ChipCE/Bear-upgrade-snakeoil-mod/4020-fan-bearmera/step/body-front.step

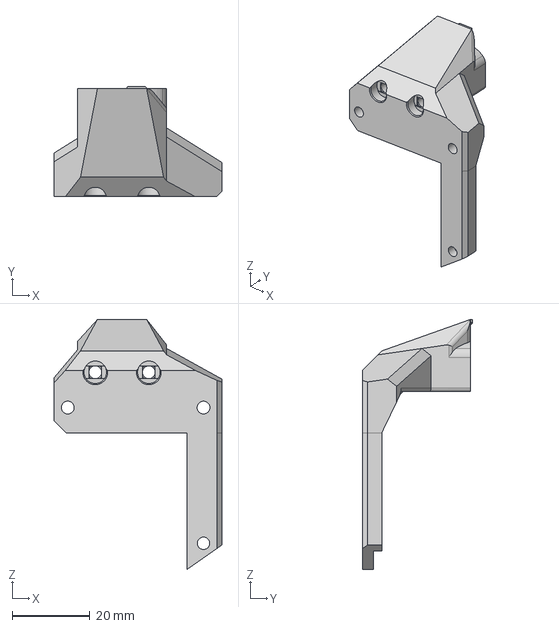
[picture p15: CAD file, 2020-04-13]
4020-fan-bearmera/step/body-front.step
43.2 x 28.4 x 64.5 mm
