ChipCE/Bear-upgrade-snakeoil-mod/BMG extruder/v2/stl/v2-hingle.stl

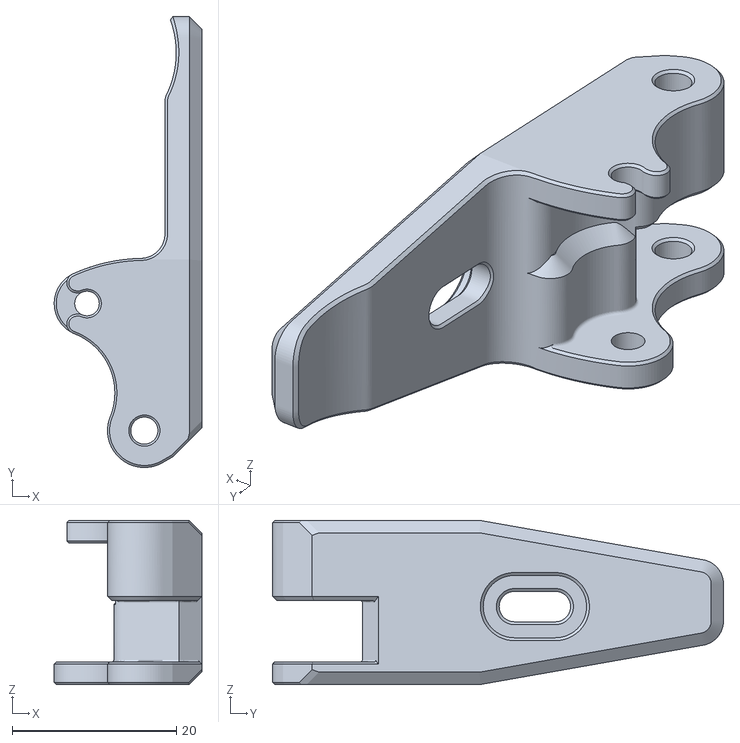
[picture p16: CAD file, 2020-04-23]
BMG extruder/v2/stl/v2-hingle.stl
18.0 x 55.0 x 20.0
