ChipCE/Bear-upgrade-snakeoil-mod/Linear-rail/Bear-frame/12h-block-mount.stl

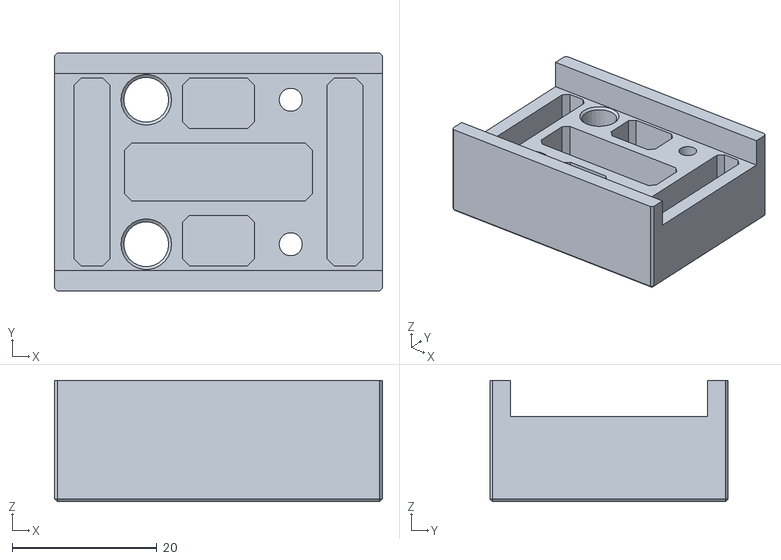
[picture p17: CAD file, 2020-05-15]
Linear-rail/Bear-frame/12h-block-mount.stl
45.4 x 33.0 x 16.8
