ChipCE/Bear-upgrade-snakeoil-mod/Linear-rail/Original-mk3-frame/v2/step/head-rev2.step

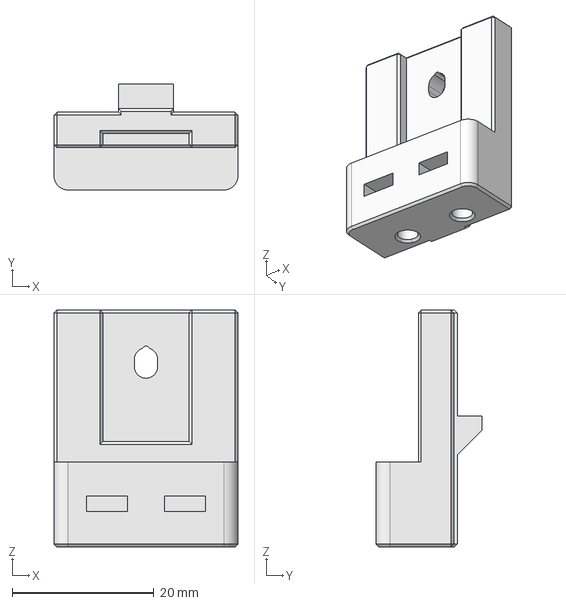
[picture p18: CAD file, 2020-04-23]
Linear-rail/Original-mk3-frame/v2/step/head-rev2.step
26.0 x 15.0 x 33.5 mm
