ChipCE/Bear-upgrade-snakeoil-mod/Y-end-stop/step/y-end-stop-cap.step

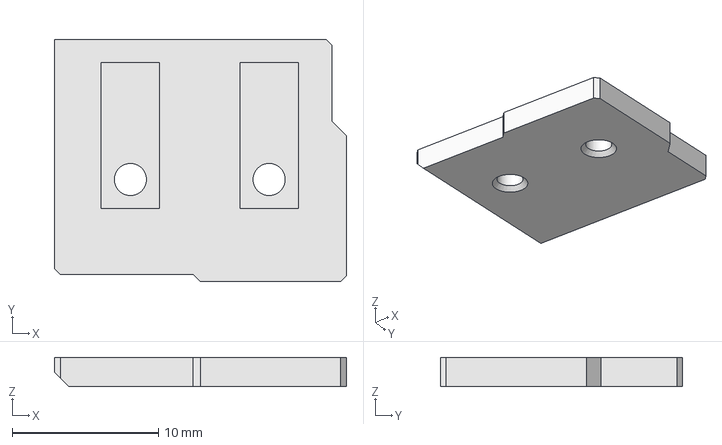
[picture p19: CAD file, 2020-04-13]
Y-end-stop/step/y-end-stop-cap.step
20.0 x 16.6 x 2.00 mm
