ChipCE/Bear-upgrade-snakeoil-mod/Y-idler-tensioner/step/base.step

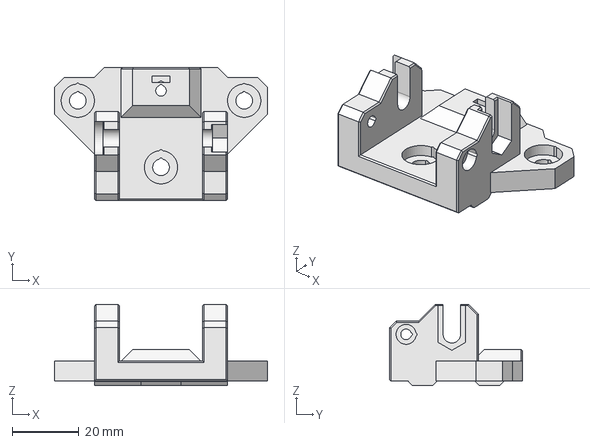
[picture p20: CAD file, 2020-04-13]
Y-idler-tensioner/step/base.step
64.0 x 40.0 x 24.4 mm
