ChipCE/Bear-upgrade-snakeoil-mod/4020-fan-bearmera/step/fan-duct.step

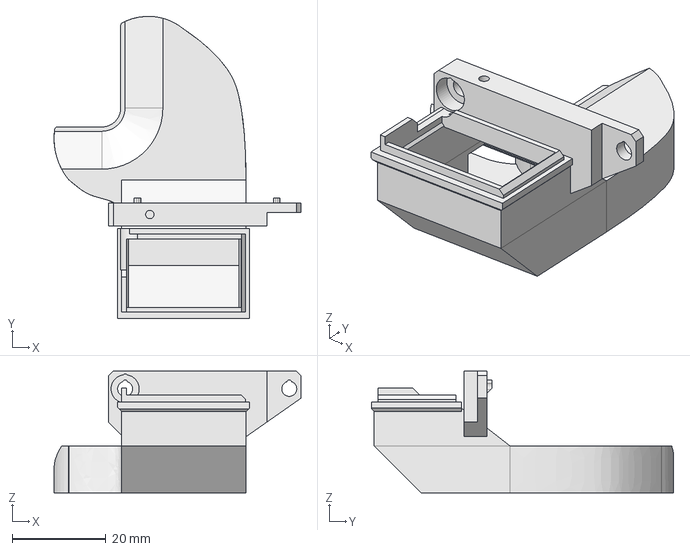
[picture p21: CAD file, 2020-04-13]
4020-fan-bearmera/step/fan-duct.step
52.7 x 64.5 x 26.0 mm
