ChipCE/Bear-upgrade-snakeoil-mod/BMG extruder/v2/stl/v2-Sensor_Cover_MK3s-M6x1.STL

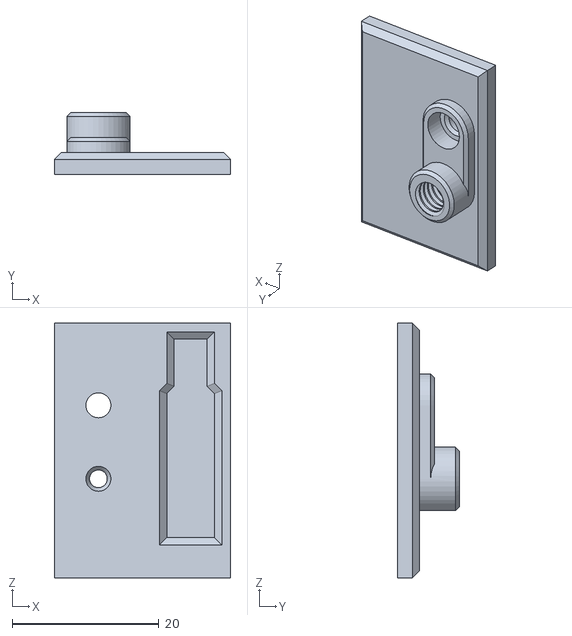
[picture p22: CAD file, 2020-04-23]
BMG extruder/v2/stl/v2-Sensor_Cover_MK3s-M6x1.STL
24.0 x 8.40 x 34.7
