ChipCE/Bear-upgrade-snakeoil-mod/Linear-rail/Bear-frame/head-tail.stl

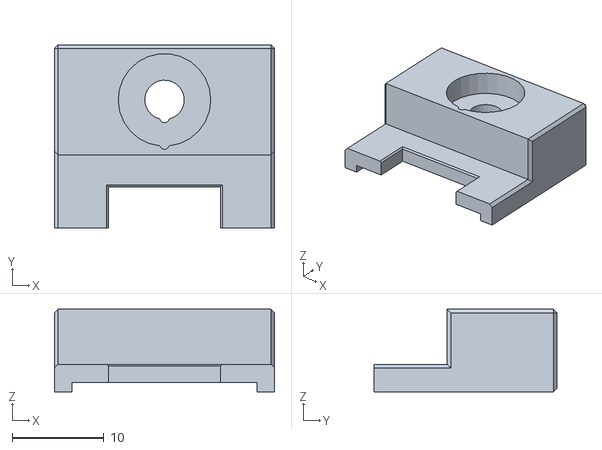
[picture p23: CAD file, 2020-04-13]
Linear-rail/Bear-frame/head-tail.stl
24.0 x 20.0 x 9.00
