ChipCE/Bear-upgrade-snakeoil-mod/Linear-rail/Original-mk3-frame/v2/step/tail-rev2.step

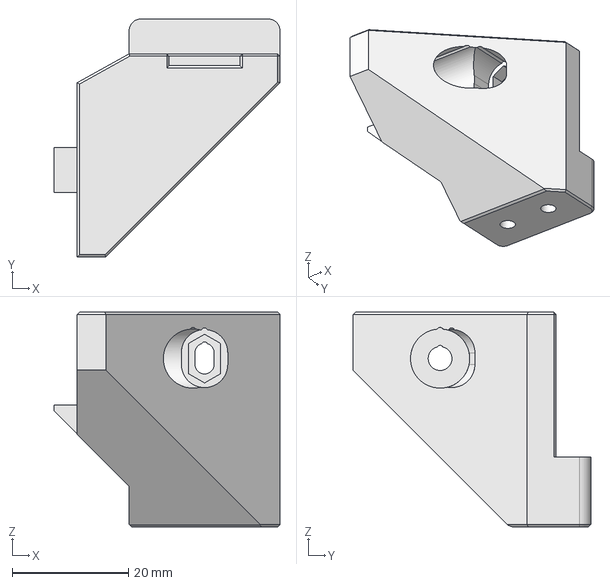
[picture p24: CAD file, 2020-04-23]
Linear-rail/Original-mk3-frame/v2/step/tail-rev2.step
39.0 x 41.0 x 37.0 mm
