ChipCE/Bear-upgrade-snakeoil-mod/BMG extruder/v2/stl/v2-adapter-printer.stl

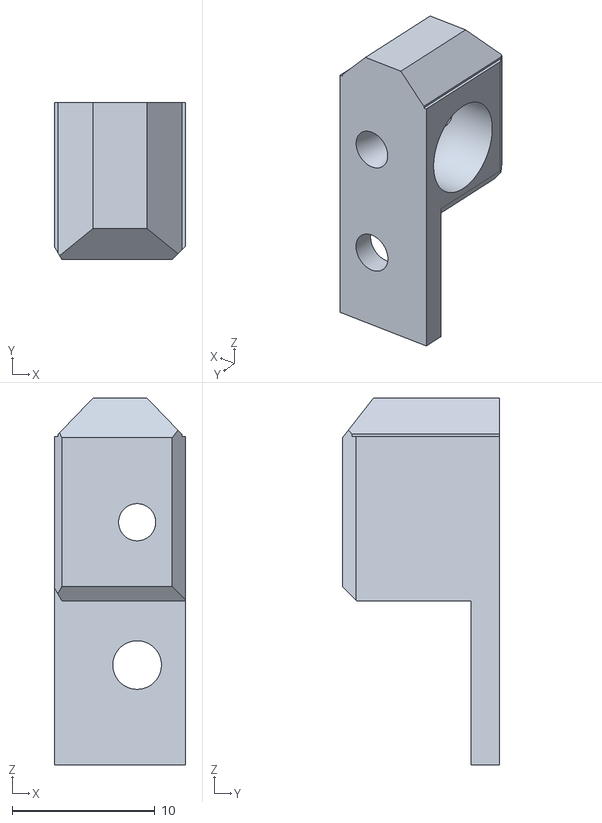
[picture p25: CAD file, 2020-04-23]
BMG extruder/v2/stl/v2-adapter-printer.stl
9.20 x 11.0 x 25.7
