ChipCE/Bear-upgrade-snakeoil-mod/BMG extruder/v2/stl/v2-ptfe-body-front..stl

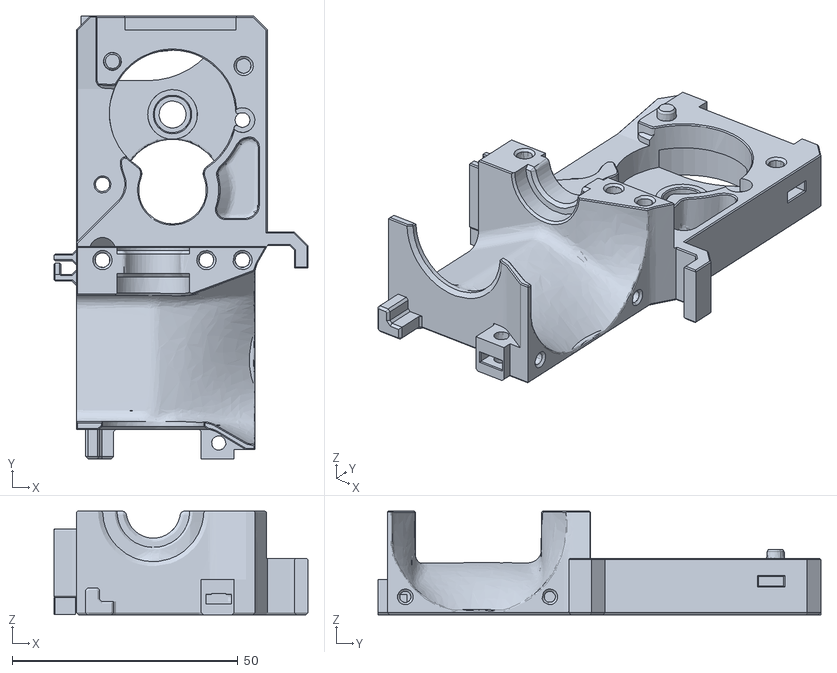
[picture p26: CAD file, 2020-04-23]
BMG extruder/v2/stl/v2-ptfe-body-front..stl
56.2 x 98.0 x 23.0
