ChipCE/Bear-upgrade-snakeoil-mod/BMG extruder/v2/stl/v2-ptfe-body-back.stl

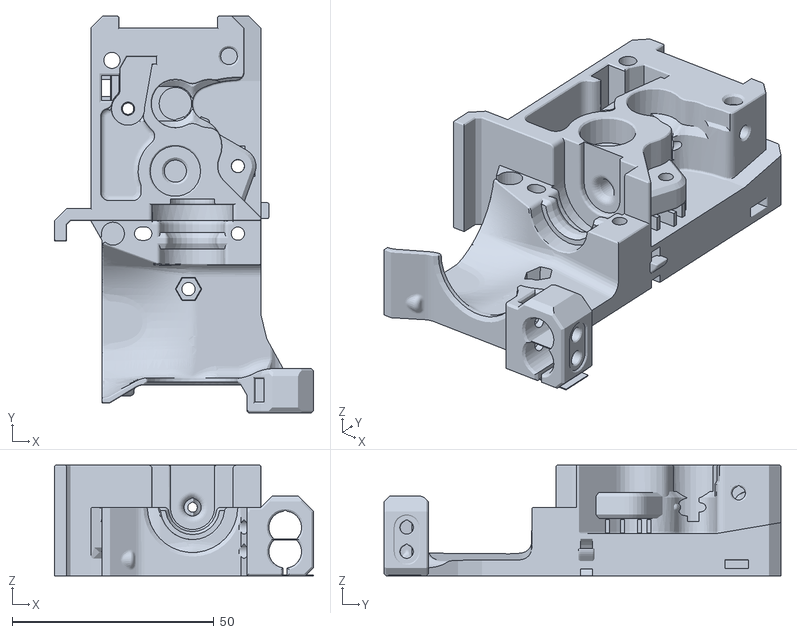
[picture p27: CAD file, 2020-04-23]
BMG extruder/v2/stl/v2-ptfe-body-back.stl
64.3 x 98.5 x 27.5
