ChipCE/Bear-upgrade-snakeoil-mod/BMG extruder/v2/stl/v2-Sensor_Cover_MK3s.stl

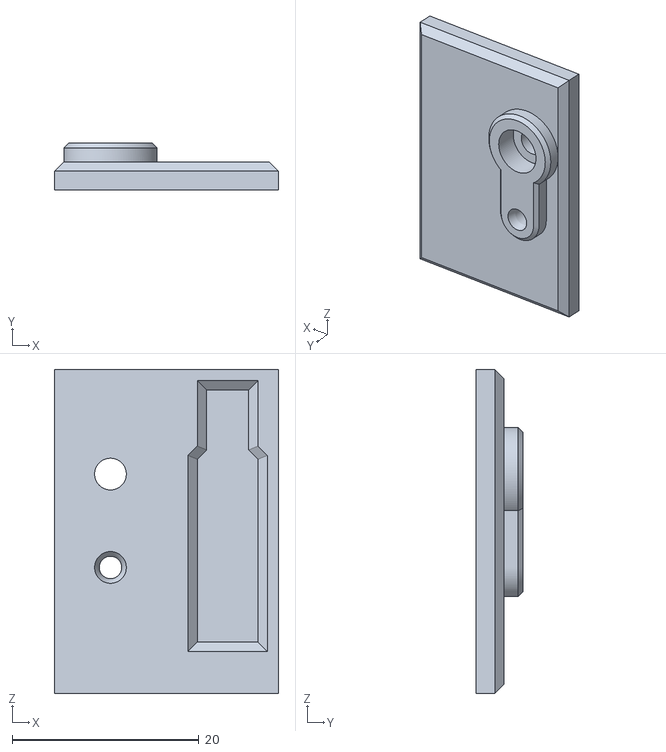
[picture p28: CAD file, 2020-04-23]
BMG extruder/v2/stl/v2-Sensor_Cover_MK3s.stl
24.0 x 5.00 x 34.7
